ChivaCable/Dise-o-mecatr-nico-Dise-o-de-un-sistema-hardware-in-the-loop-para-un-Robot-manipulador-serial-RR/Archivos PCB/Archivos Visuales/PCB vista inferior.png

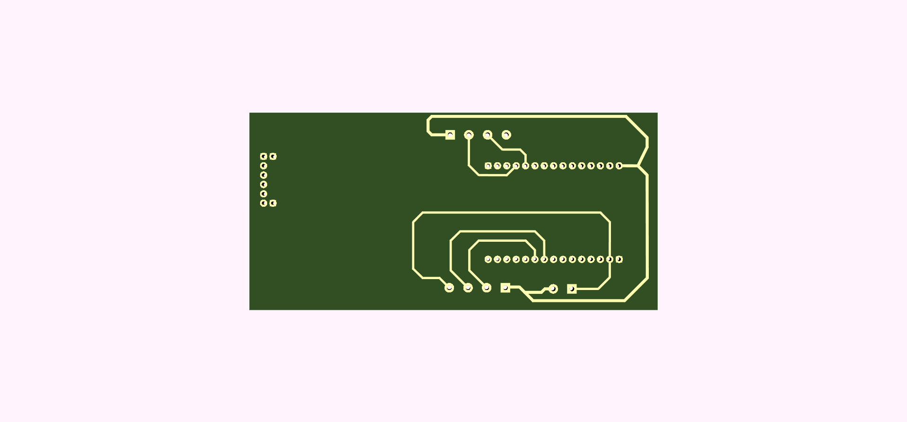
Archivos PCB/Archivos Visuales/PCB vista inferior.png
