ChivaCable/Dise-o-mecatr-nico-Dise-o-de-un-sistema-hardware-in-the-loop-para-un-Robot-manipulador-serial-RR/Archivos PCB/Archivos Visuales/Reprecentacion visual de las conexiones del circuito.png

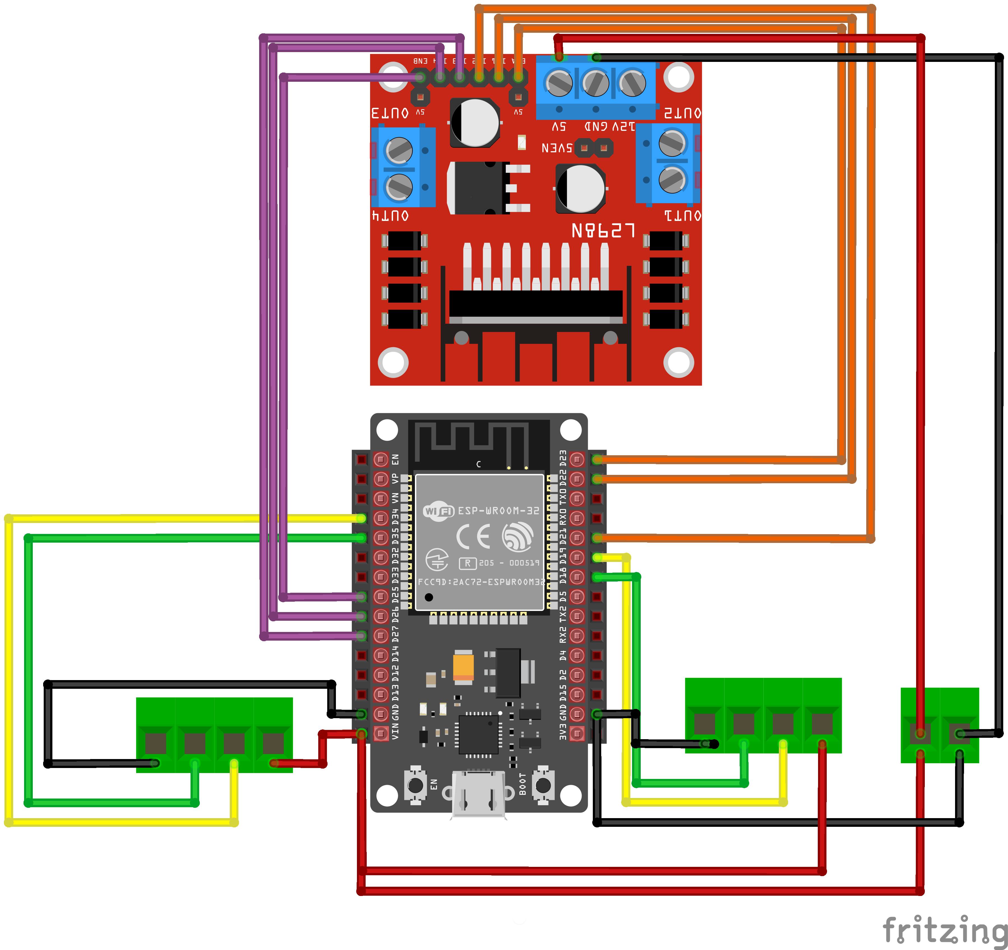
Archivos PCB/Archivos Visuales/Reprecentacion visual de las conexiones del circuito.png
