ChivaCable/Dise-o-mecatr-nico-Dise-o-de-un-sistema-hardware-in-the-loop-para-un-Robot-manipulador-serial-RR/Estructura/Piezas/dm37 motor.png

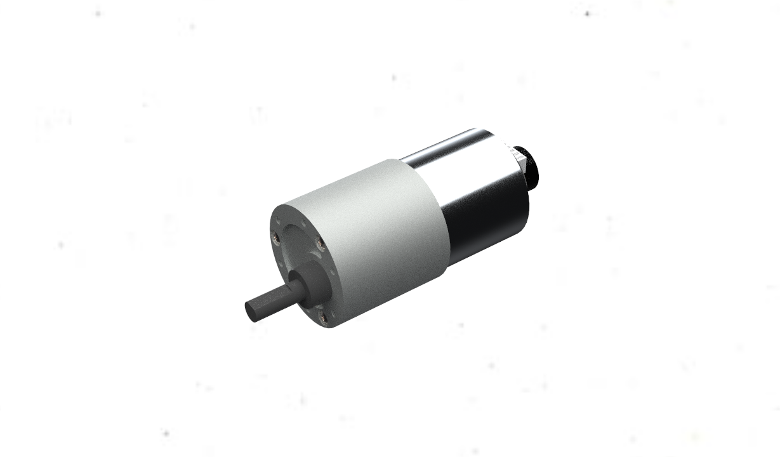
Estructura/Piezas/dm37 motor.png
