ChivaCable/Dise-o-mecatr-nico-Dise-o-de-un-sistema-hardware-in-the-loop-para-un-Robot-manipulador-serial-RR/Estructura/Piezas/dm bone 1.png

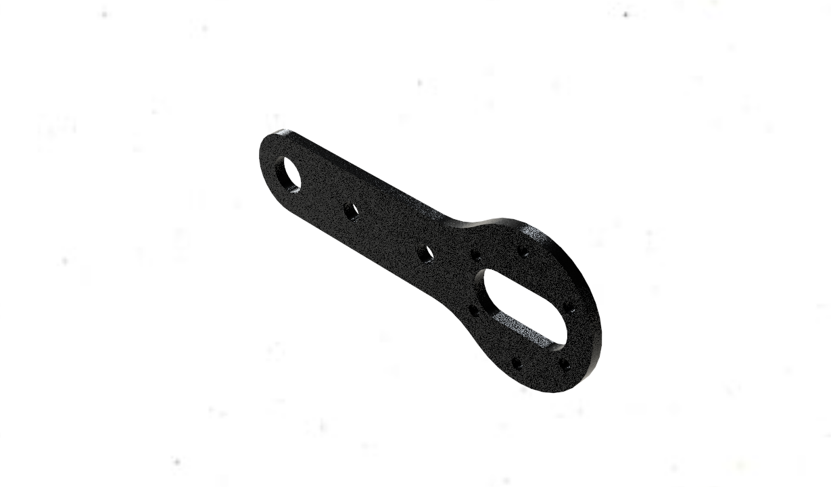
Estructura/Piezas/dm bone 1.png
