ChivaCable/Dise-o-mecatr-nico-Dise-o-de-un-sistema-hardware-in-the-loop-para-un-Robot-manipulador-serial-RR/Estructura/Planos/DMBone2.PNG

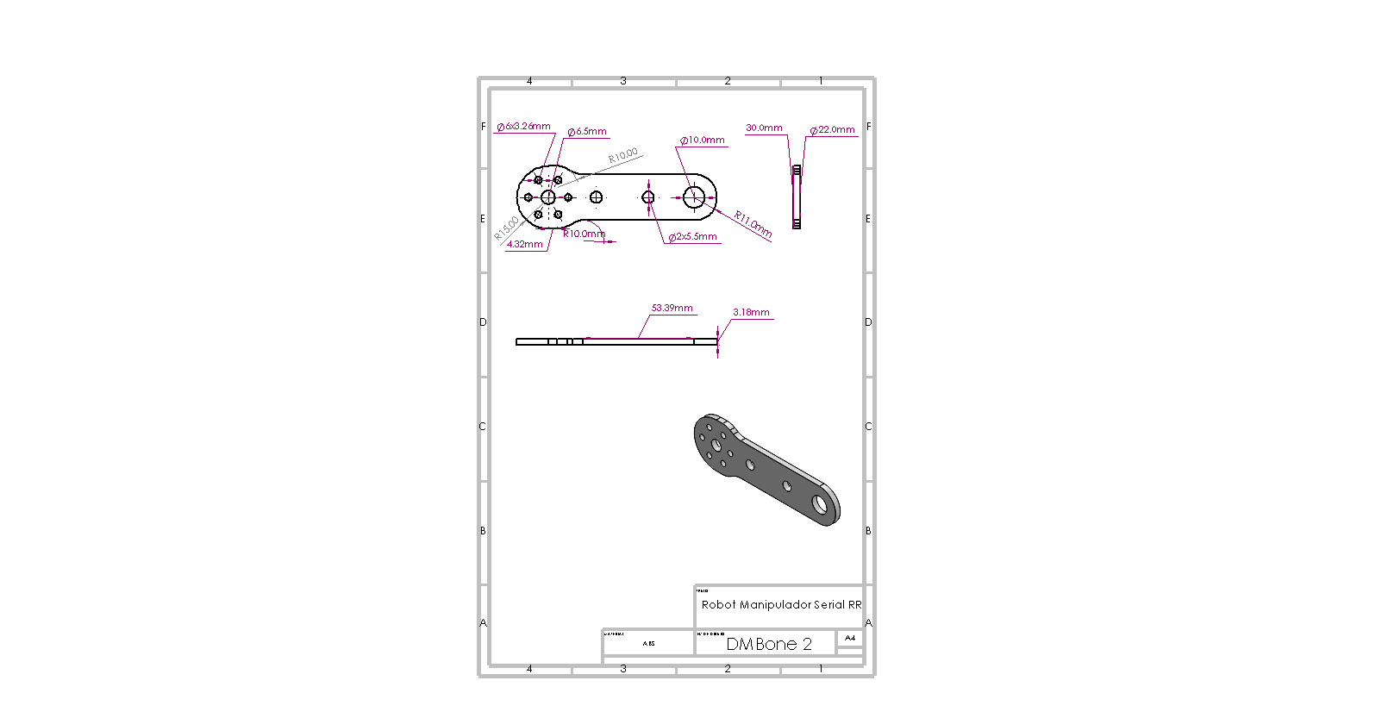
Estructura/Planos/DMBone2.PNG
