ChivaCable/Dise-o-mecatr-nico-Dise-o-de-un-sistema-hardware-in-the-loop-para-un-Robot-manipulador-serial-RR/Estructura/Planos/DMLaminaGripper.PNG

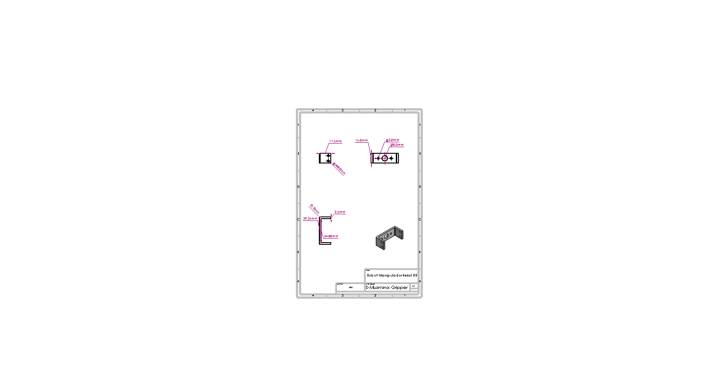
Estructura/Planos/DMLaminaGripper.PNG
