ChivaCable/Dise-o-mecatr-nico-Dise-o-de-un-sistema-hardware-in-the-loop-para-un-Robot-manipulador-serial-RR/Estructura/Planos/DMPieza2.PNG

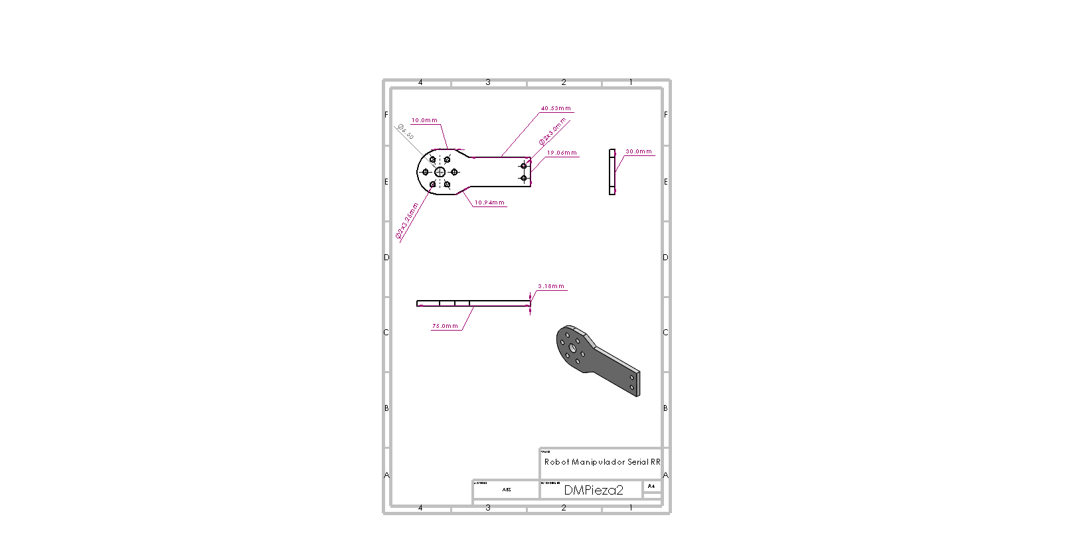
Estructura/Planos/DMPieza2.PNG
