ChivaCable/Dise-o-mecatr-nico-Dise-o-de-un-sistema-hardware-in-the-loop-para-un-Robot-manipulador-serial-RR/Estructura/Planos/DMPot.PNG

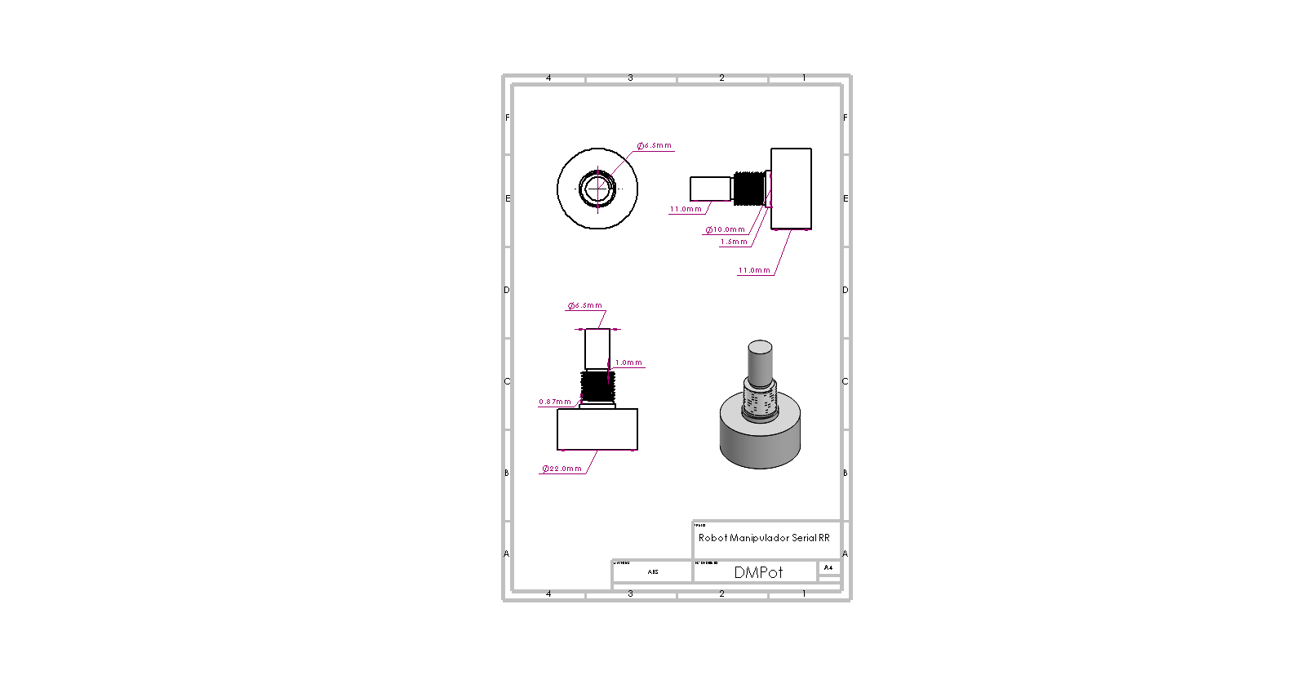
Estructura/Planos/DMPot.PNG
