ChivaCable/Dise-o-mecatr-nico-Dise-o-de-un-sistema-hardware-in-the-loop-para-un-Robot-manipulador-serial-RR/Estructura/SolidWorks/Ensamblaje1.1.SLDASM

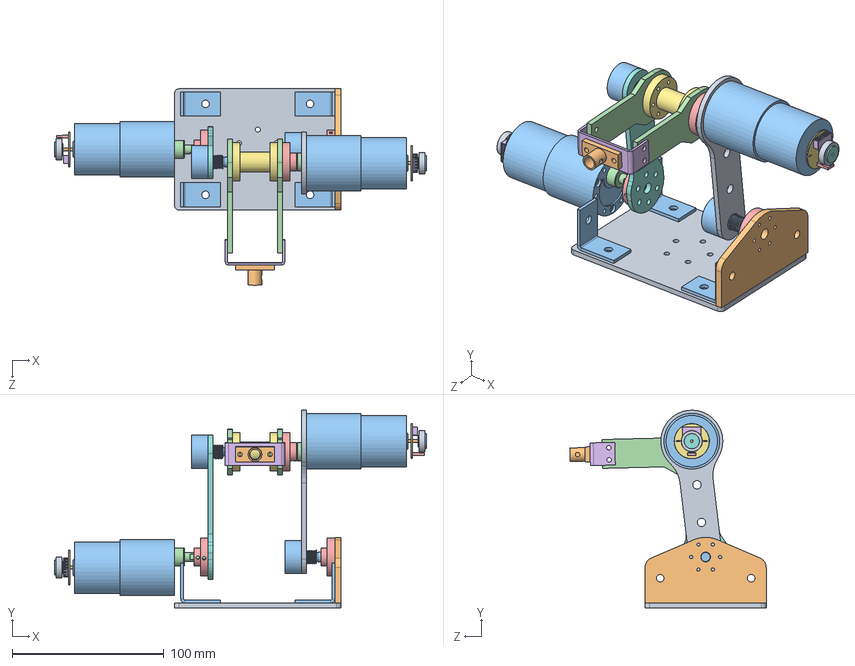
[picture p35: CAD file, 2025-05-23]
Estructura/SolidWorks/Ensamblaje1.1.SLDASM
245.5 x 130.5 x 129.7 mm
DM37D Body x 2
DMMotorshaft x 2
DMEncoder Magnet x 2
DMEncoder Spindle x 2
DMEncoder PCB x 2
DMEncoder Terminal x 2
DMEncoder Hall Effect Sensor x 2
DMGear Shaft x 2
DMAngulo x 4
DMApoyo V2.1
DMArm Base
DMBone 2
DMDouble Cople
DMLamina Gripper
DMMotor Cople x 3
DMPieza2 x 2
DMpot x 2
End Effector
DMApoyo Motor1.1
