ChivaCable/Dise-o-mecatr-nico-Dise-o-de-un-sistema-hardware-in-the-loop-para-un-Robot-manipulador-serial-RR/Estructura/SolidWorks/Parte3/p3DMPieza2.SLDPRT

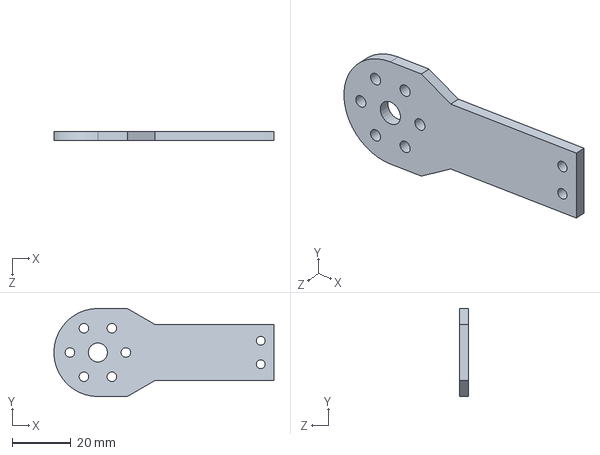
[picture p42: CAD file, 2025-05-23]
Estructura/SolidWorks/Parte3/p3DMPieza2.SLDPRT
75.0 x 30.0 x 3.17 mm
