ChivaCable/Dise-o-mecatr-nico-Dise-o-de-un-sistema-hardware-in-the-loop-para-un-Robot-manipulador-serial-RR/my_robot_planar/meshes/Motor2_Link.STL

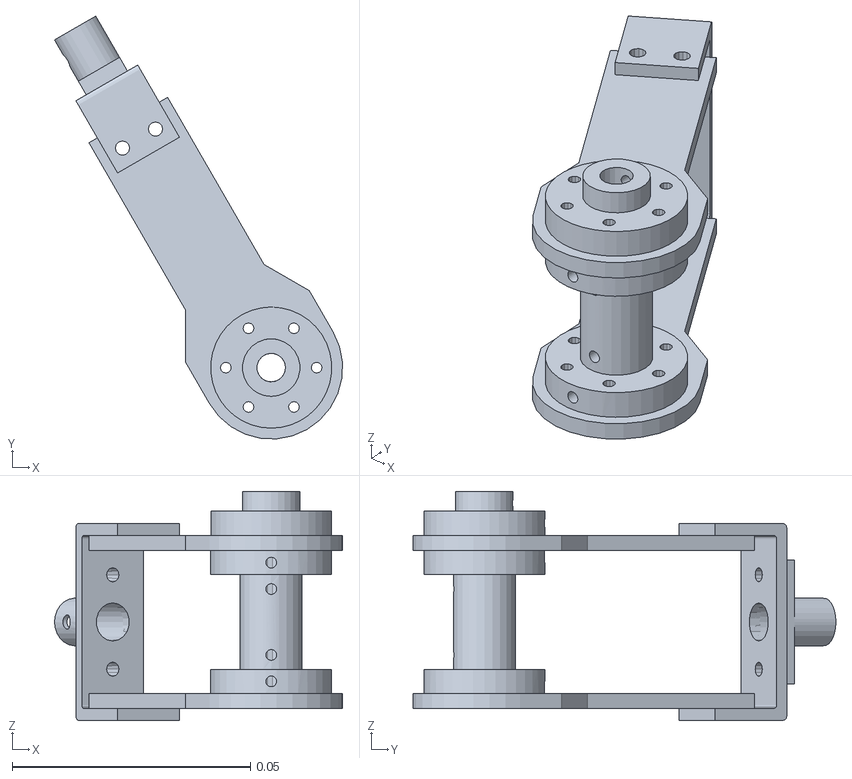
[picture p43: CAD file, 2025-05-23]
my_robot_planar/meshes/Motor2_Link.STL
0.0604 x 0.0887 x 0.0481
