ChivaCable/Dise-o-mecatr-nico-Dise-o-de-un-sistema-hardware-in-the-loop-para-un-Robot-manipulador-serial-RR/Estructura/SolidWorks/DMEncoder Terminal.SLDPRT

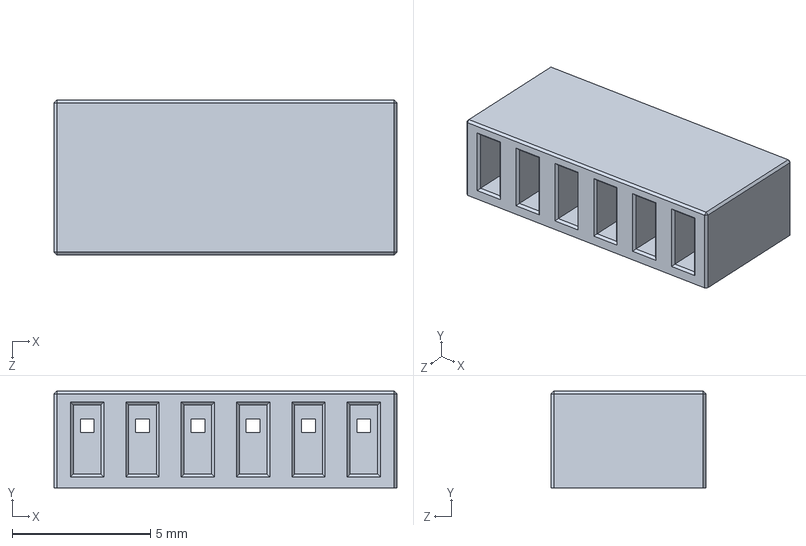
[picture p44: CAD file, 2025-05-23]
Estructura/SolidWorks/DMEncoder Terminal.SLDPRT
12.4 x 3.50 x 5.60 mm
