ChivaCable/Dise-o-mecatr-nico-Dise-o-de-un-sistema-hardware-in-the-loop-para-un-Robot-manipulador-serial-RR/Estructura/SolidWorks/Parte 2/DMEncoder Magnet.SLDPRT

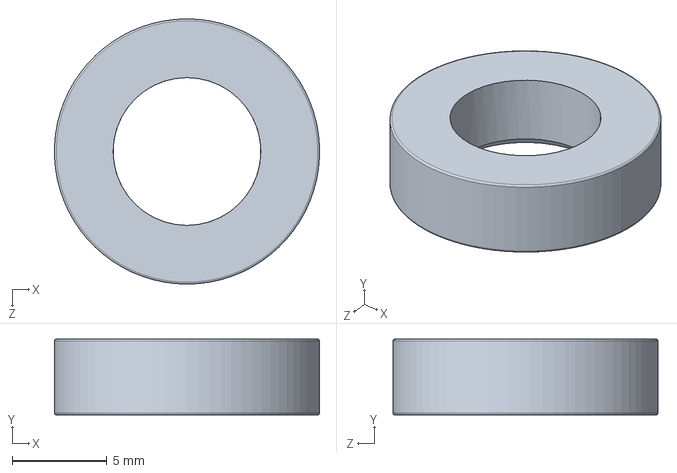
[picture p45: CAD file, 2025-05-23]
Estructura/SolidWorks/Parte 2/DMEncoder Magnet.SLDPRT
14.0 x 4.00 x 14.0 mm
