ChivaCable/Dise-o-mecatr-nico-Dise-o-de-un-sistema-hardware-in-the-loop-para-un-Robot-manipulador-serial-RR/my_robot_planar/meshes/Motor1_Link.STL

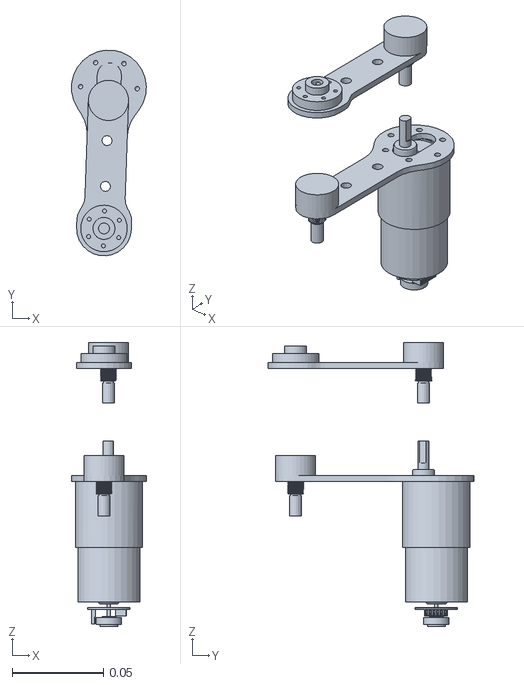
[picture p46: CAD file, 2025-05-23]
my_robot_planar/meshes/Motor1_Link.STL
0.0409 x 0.112 x 0.155
