ChivaCable/Dise-o-mecatr-nico-Dise-o-de-un-sistema-hardware-in-the-loop-para-un-Robot-manipulador-serial-RR/Estructura/SolidWorks/DMApoyo V2.1.SLDPRT

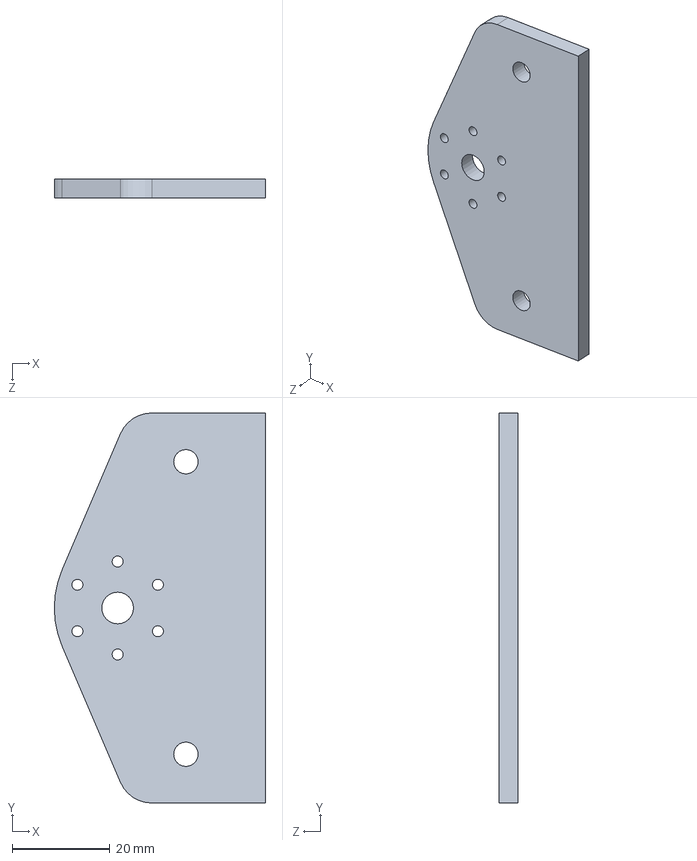
[picture p47: CAD file, 2025-05-23]
Estructura/SolidWorks/DMApoyo V2.1.SLDPRT
43.4 x 80.0 x 4.00 mm
