ChivaCable/Dise-o-mecatr-nico-Dise-o-de-un-sistema-hardware-in-the-loop-para-un-Robot-manipulador-serial-RR/Estructura/SolidWorks/Parte 2/DMEncoder Hall Effect Sensor.SLDPRT

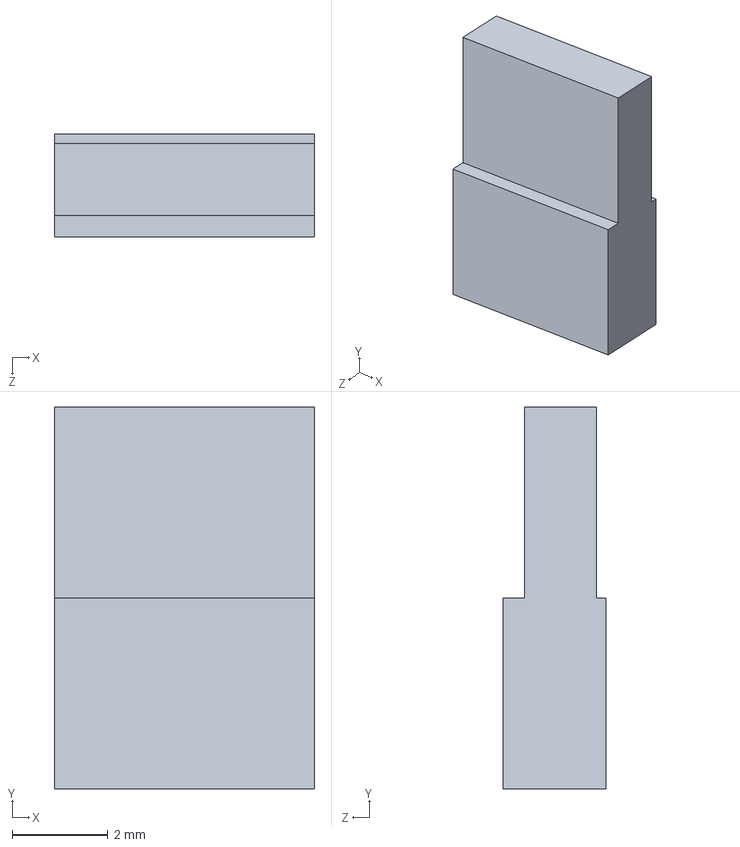
[picture p48: CAD file, 2025-05-23]
Estructura/SolidWorks/Parte 2/DMEncoder Hall Effect Sensor.SLDPRT
5.45 x 8.00 x 2.15 mm
