ChivaCable/Dise-o-mecatr-nico-Dise-o-de-un-sistema-hardware-in-the-loop-para-un-Robot-manipulador-serial-RR/Estructura/SolidWorks/Parte3/p3End Effector.SLDPRT

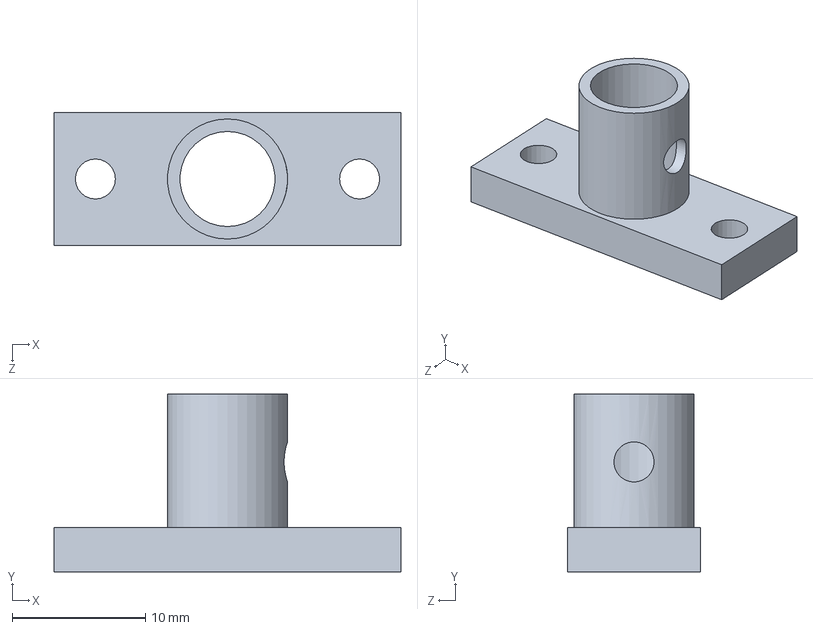
[picture p49: CAD file, 2025-05-23]
Estructura/SolidWorks/Parte3/p3End Effector.SLDPRT
26.0 x 13.3 x 10.0 mm
