ChivaCable/Dise-o-mecatr-nico-Dise-o-de-un-sistema-hardware-in-the-loop-para-un-Robot-manipulador-serial-RR/Estructura/SolidWorks/DMMotorshaft.SLDPRT

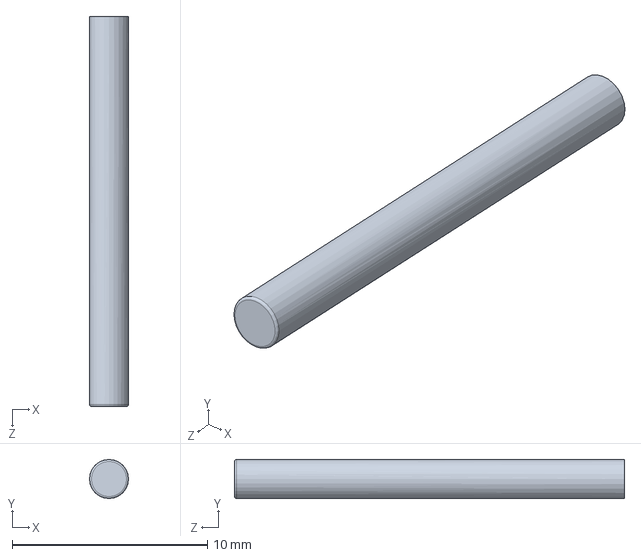
[picture p50: CAD file, 2025-05-23]
Estructura/SolidWorks/DMMotorshaft.SLDPRT
2.00 x 2.00 x 20.0 mm
