ChivaCable/Dise-o-mecatr-nico-Dise-o-de-un-sistema-hardware-in-the-loop-para-un-Robot-manipulador-serial-RR/Estructura/SolidWorks/Parte 2/DMGear Shaft.SLDPRT

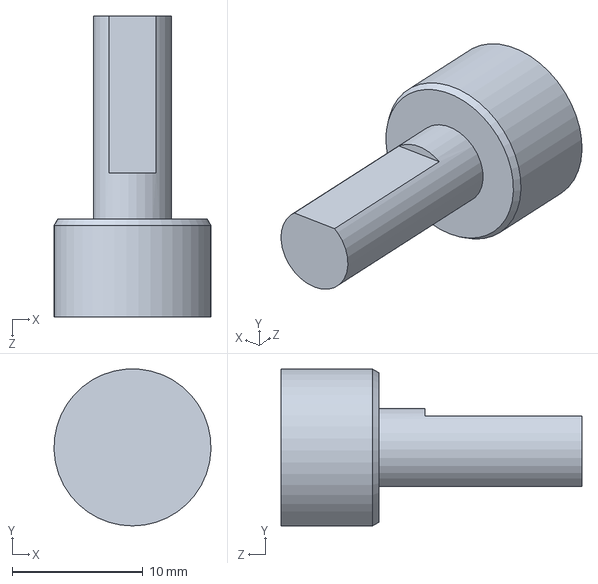
[picture p51: CAD file, 2025-05-23]
Estructura/SolidWorks/Parte 2/DMGear Shaft.SLDPRT
12.0 x 12.0 x 23.0 mm
