ChivaCable/Dise-o-mecatr-nico-Dise-o-de-un-sistema-hardware-in-the-loop-para-un-Robot-manipulador-serial-RR/Estructura/SolidWorks/Parte3/p3DMLamina Gripper.SLDPRT

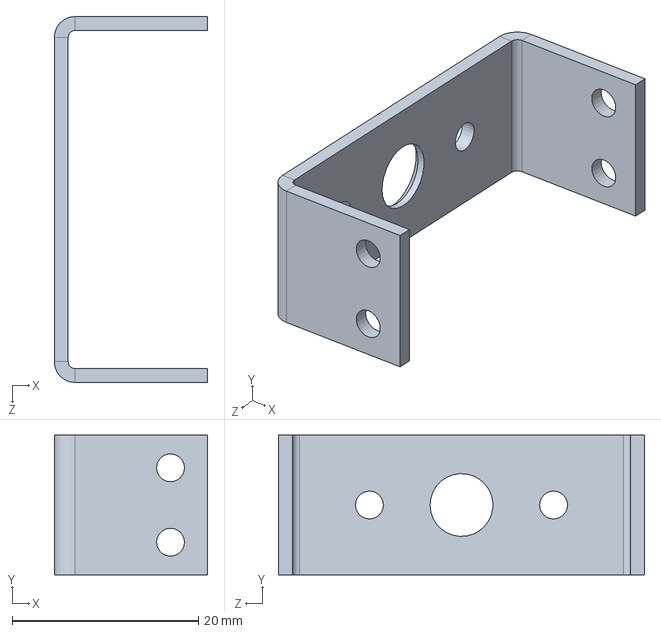
[picture p52: CAD file, 2025-05-23]
Estructura/SolidWorks/Parte3/p3DMLamina Gripper.SLDPRT
16.5 x 15.0 x 39.3 mm
