ChivaCable/Dise-o-mecatr-nico-Dise-o-de-un-sistema-hardware-in-the-loop-para-un-Robot-manipulador-serial-RR/Estructura/SolidWorks/DMBone 2.SLDPRT

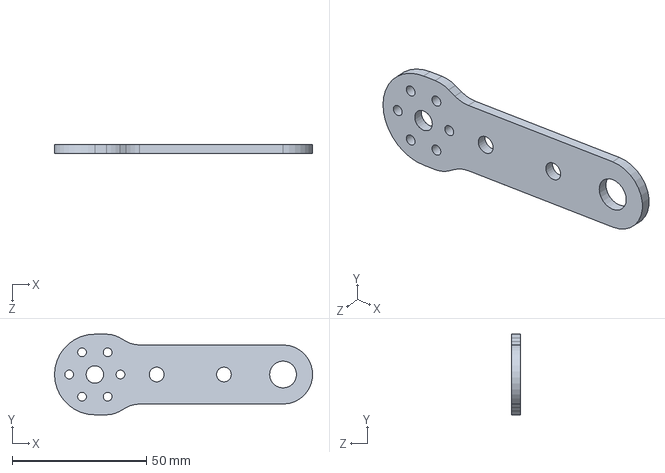
[picture p53: CAD file, 2025-05-23]
Estructura/SolidWorks/DMBone 2.SLDPRT
95.9 x 30.0 x 3.17 mm
