ChivaCable/Dise-o-mecatr-nico-Dise-o-de-un-sistema-hardware-in-the-loop-para-un-Robot-manipulador-serial-RR/Estructura/SolidWorks/Apoyo Motor.SLDPRT

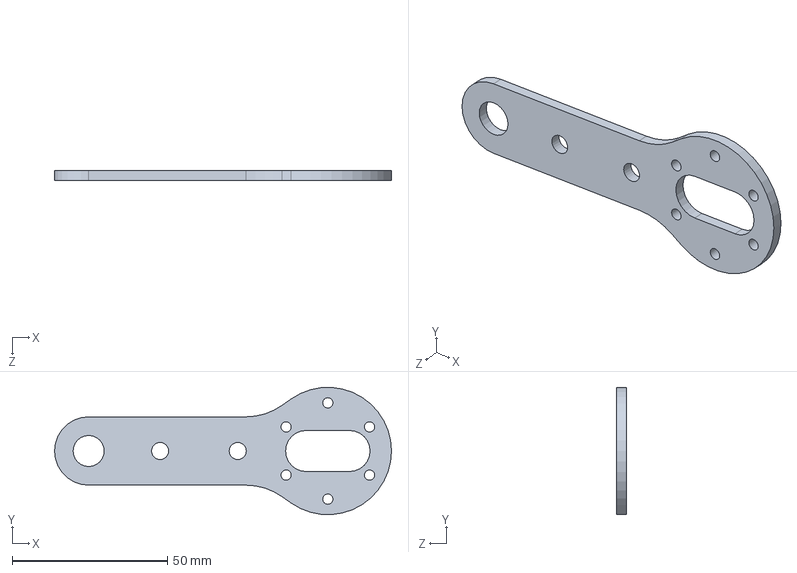
[picture p54: CAD file, 2025-05-23]
Estructura/SolidWorks/Apoyo Motor.SLDPRT
108.5 x 40.9 x 3.17 mm
