ChivaCable/Dise-o-mecatr-nico-Dise-o-de-un-sistema-hardware-in-the-loop-para-un-Robot-manipulador-serial-RR/Estructura/SolidWorks/Parte 2/DM37D Body.SLDPRT

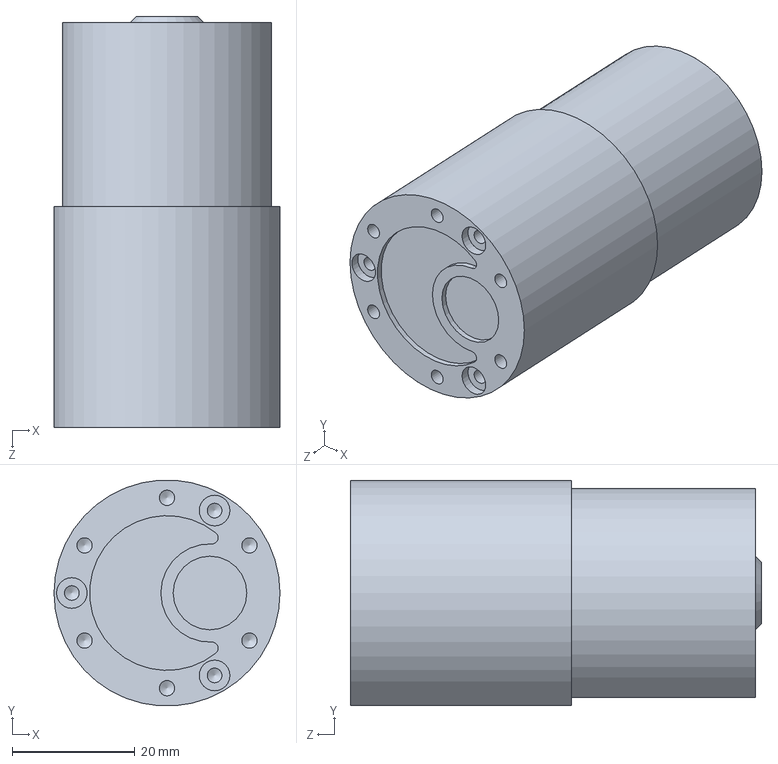
[picture p55: CAD file, 2025-05-23]
Estructura/SolidWorks/Parte 2/DM37D Body.SLDPRT
36.8 x 36.7 x 67.0 mm
