ChivaCable/Dise-o-mecatr-nico-Dise-o-de-un-sistema-hardware-in-the-loop-para-un-Robot-manipulador-serial-RR/Estructura/SolidWorks/DMAngulo.SLDPRT

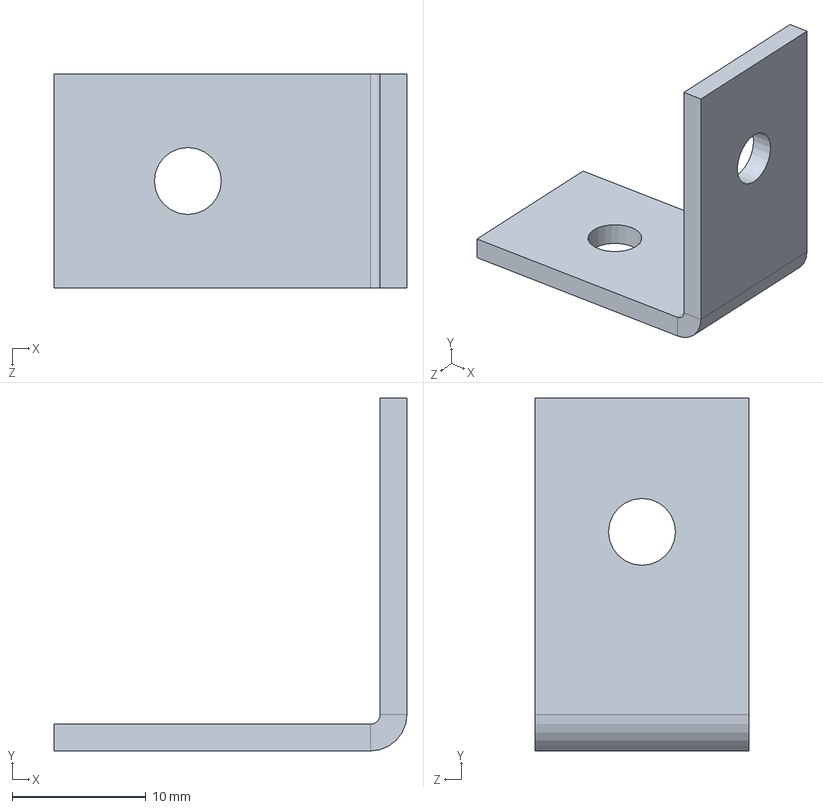
[picture p56: CAD file, 2025-05-23]
Estructura/SolidWorks/DMAngulo.SLDPRT
26.4 x 26.4 x 16.0 mm
