ChivaCable/Dise-o-mecatr-nico-Dise-o-de-un-sistema-hardware-in-the-loop-para-un-Robot-manipulador-serial-RR/Estructura/SolidWorks/Parte 2/DMEncoder PCB.SLDPRT

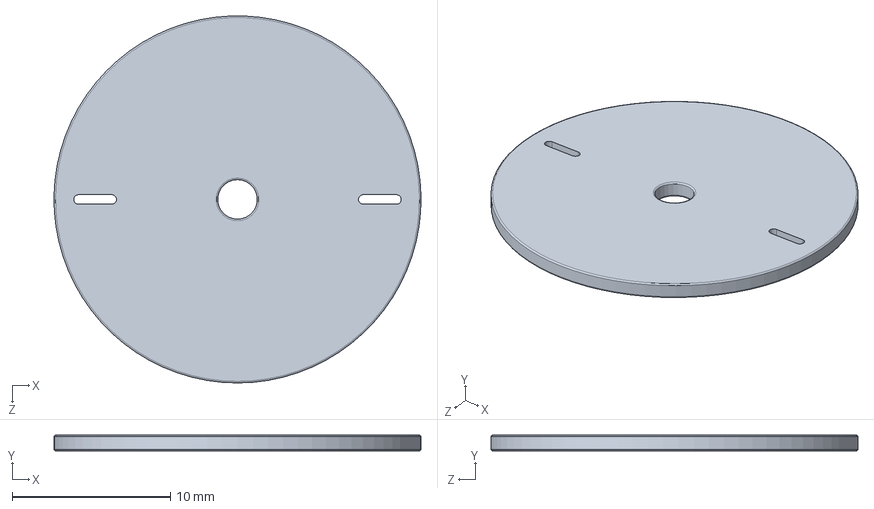
[picture p57: CAD file, 2025-05-23]
Estructura/SolidWorks/Parte 2/DMEncoder PCB.SLDPRT
23.2 x 1.00 x 23.2 mm
