ChivaCable/Dise-o-mecatr-nico-Dise-o-de-un-sistema-hardware-in-the-loop-para-un-Robot-manipulador-serial-RR/Estructura/SolidWorks/DMArm Base.SLDPRT

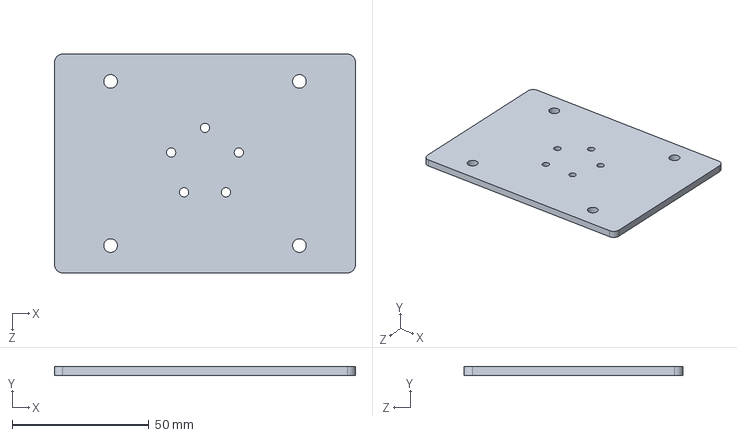
[picture p58: CAD file, 2025-05-23]
Estructura/SolidWorks/DMArm Base.SLDPRT
110.0 x 3.17 x 80.0 mm
