ChivaCable/Dise-o-mecatr-nico-Dise-o-de-un-sistema-hardware-in-the-loop-para-un-Robot-manipulador-serial-RR/Estructura/SolidWorks/Partegod1.SLDPRT

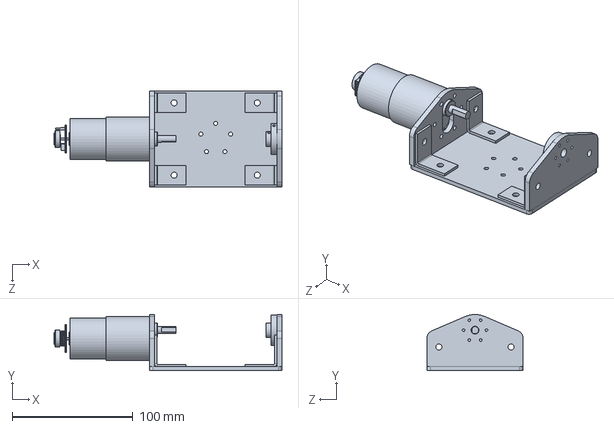
[picture p59: CAD file, 2025-05-23]
Estructura/SolidWorks/Partegod1.SLDPRT
189.2 x 46.5 x 80.0 mm
